Ahmed-Husseini/Automated-Robot-Arm/Media/1.jpg

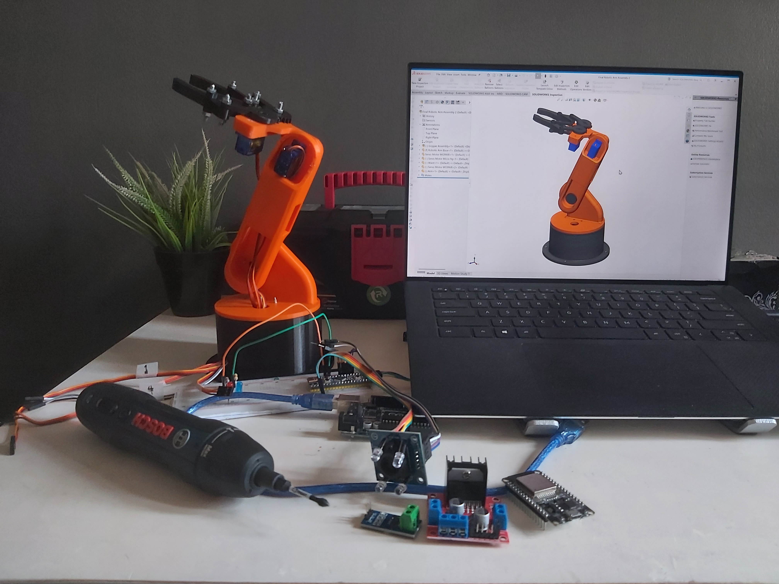
Media/1.jpg
