Ahmed-Husseini/Automated-Robot-Arm/Media/2.jpg

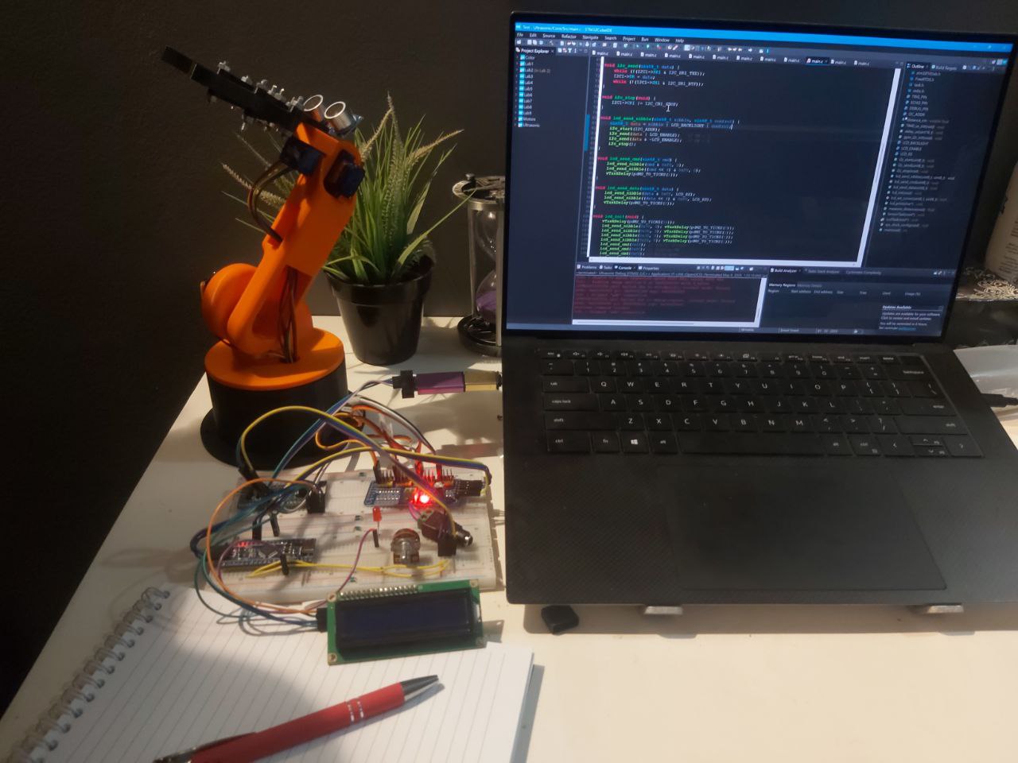
Media/2.jpg
