Ahmed-Husseini/Automated-Robot-Arm/Media/7.jpg

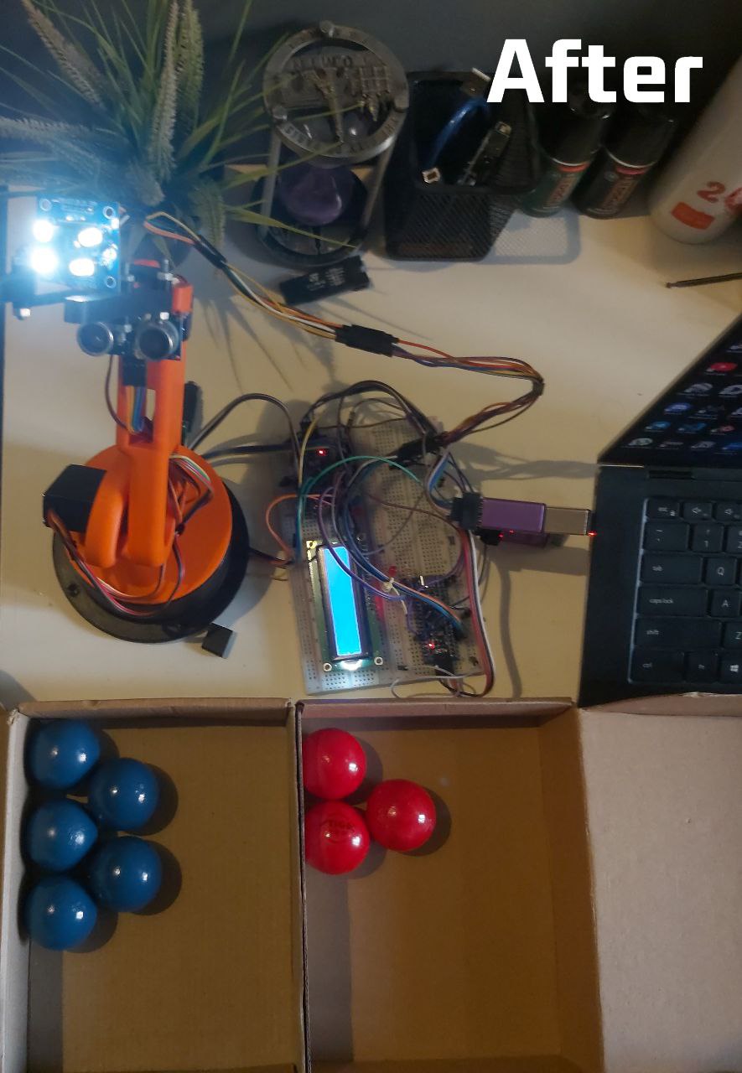
Media/7.jpg
