Ahmed-Husseini/Automated-Robot-Arm/Model/Images/Drawing.JPG

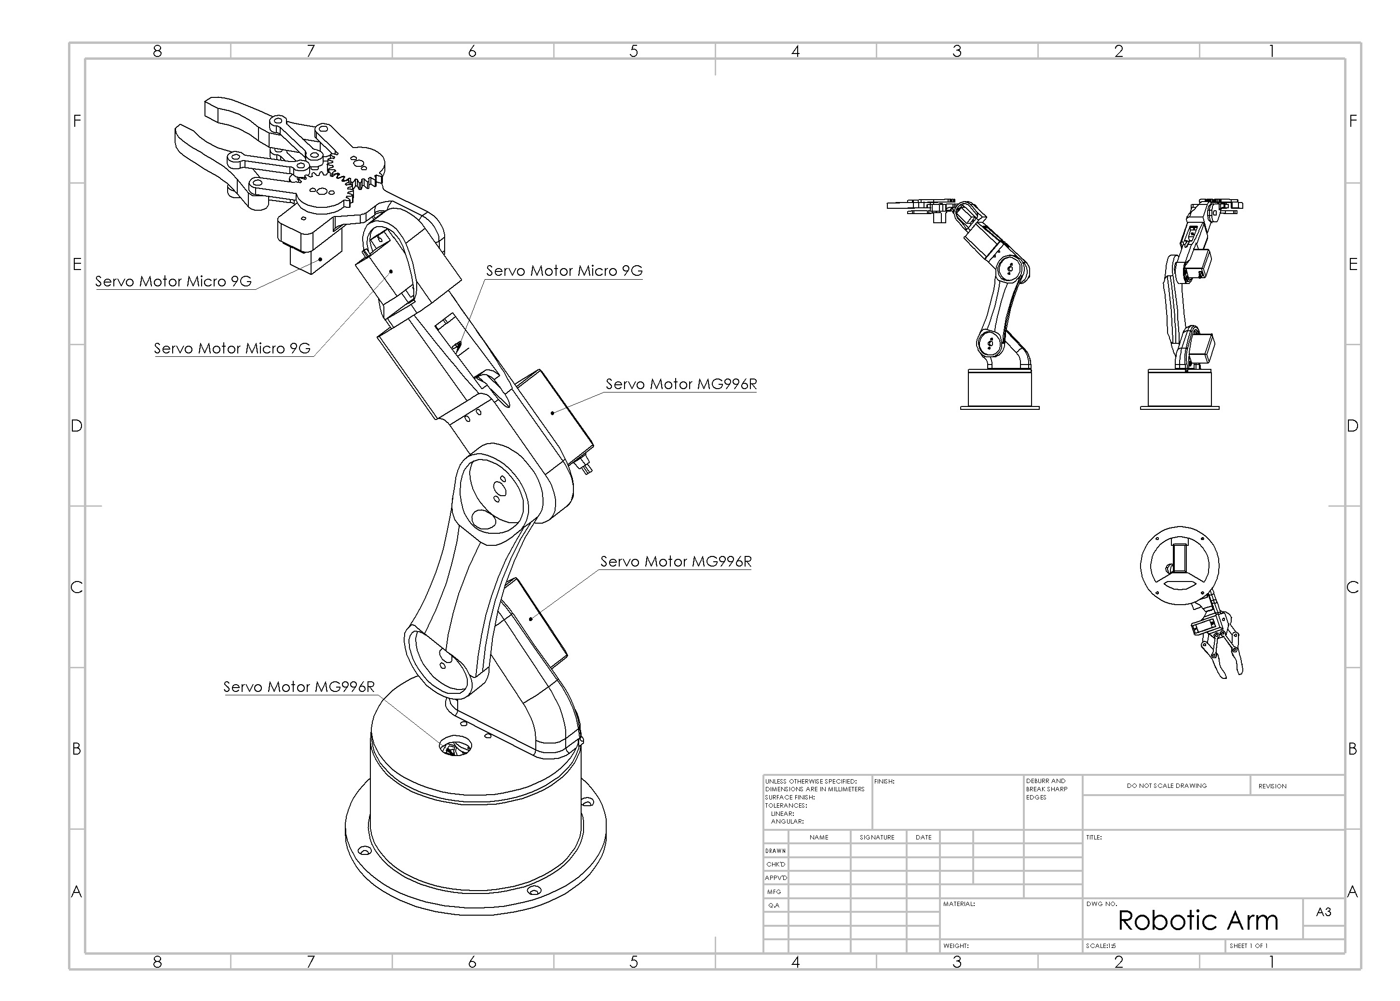
Model/Images/Drawing.JPG
