Ahmed-Husseini/Automated-Robot-Arm/Model/STL Files/Gripper 1.STL

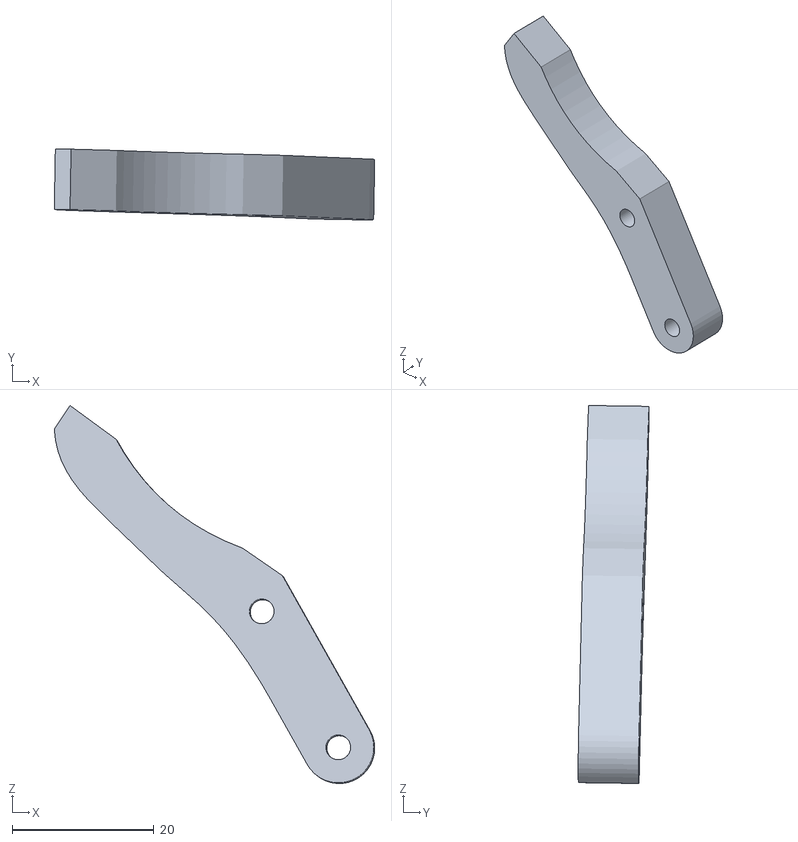
[picture p42: CAD file, 2025-07-17]
Model/STL Files/Gripper 1.STL
45.2 x 9.97 x 53.3
