Ahmed-Husseini/Automated-Robot-Arm/Model/Servo Motor Micro 9g.SLDPRT

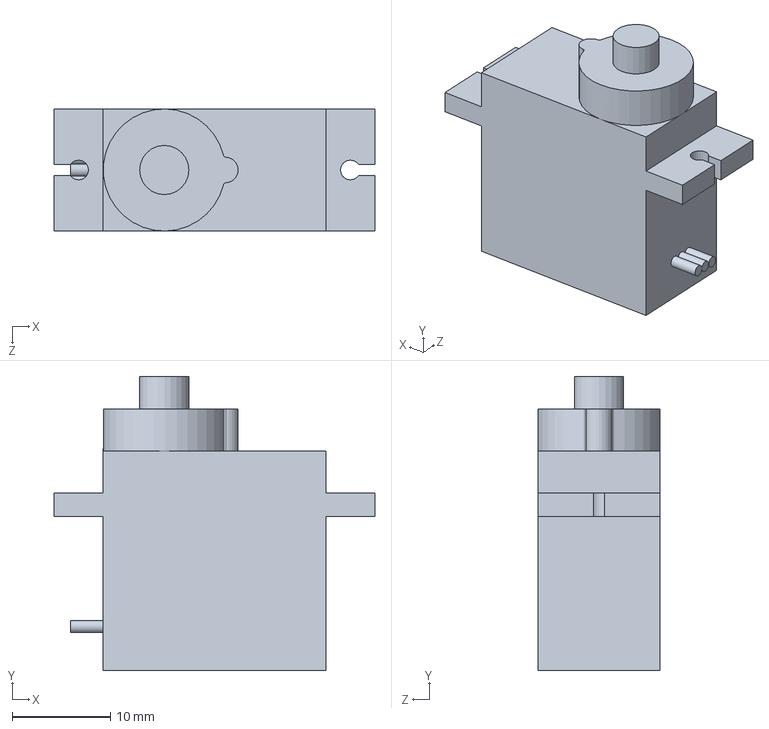
[picture p43: CAD file, 2025-07-17]
Model/Servo Motor Micro 9g.SLDPRT
32.6 x 29.9 x 12.4 mm
