Ahmed-Husseini/Automated-Robot-Arm/Model/Arm 3.SLDPRT

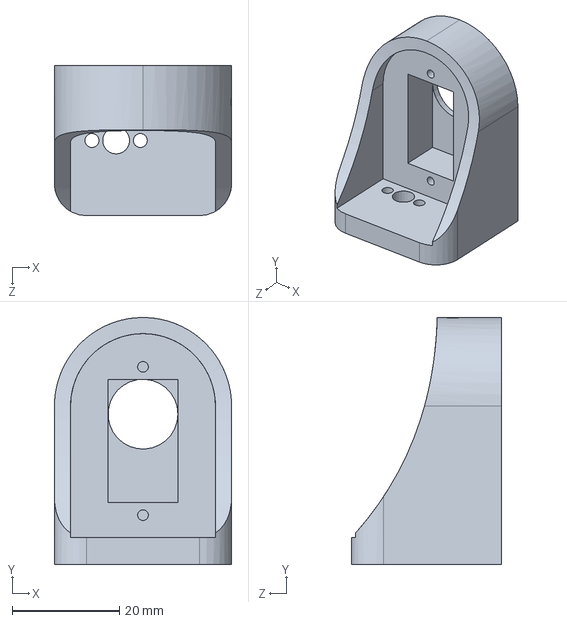
[picture p44: CAD file, 2025-07-17]
Model/Arm 3.SLDPRT
33.0 x 46.0 x 28.0 mm
