Ahmed-Husseini/Automated-Robot-Arm/Model/Arm 2.SLDPRT

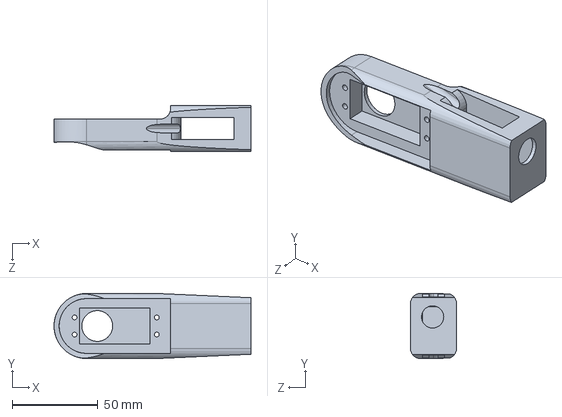
[picture p45: CAD file, 2025-07-17]
Model/Arm 2.SLDPRT
115.0 x 38.0 x 27.0 mm
