Ahmed-Husseini/Automated-Robot-Arm/Model/Waist.SLDPRT

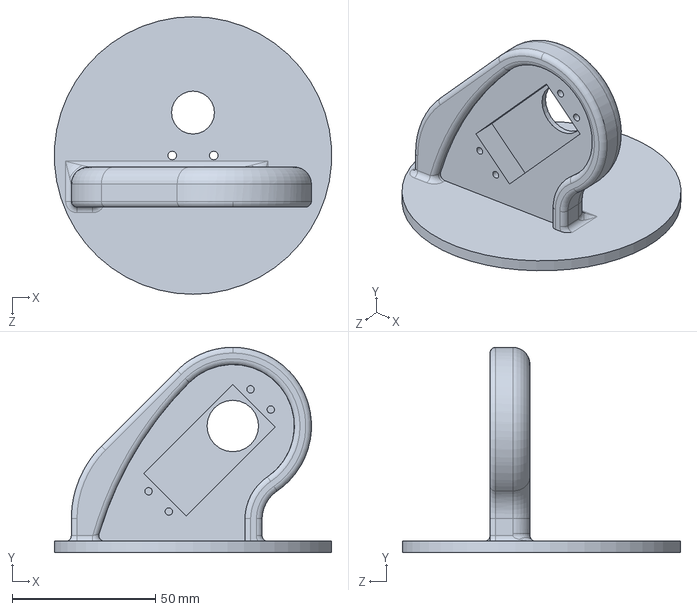
[picture p46: CAD file, 2025-07-17]
Model/Waist.SLDPRT
96.8 x 71.8 x 97.0 mm
