Ahmed-Husseini/Automated-Robot-Arm/Model/Arm 1.SLDPRT

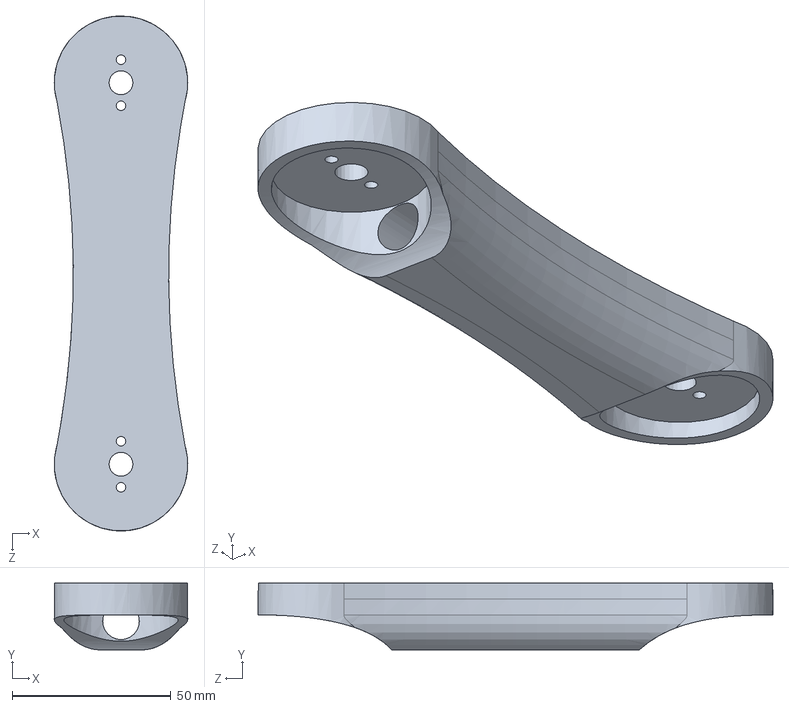
[picture p47: CAD file, 2025-07-17]
Model/Arm 1.SLDPRT
42.0 x 21.0 x 162.0 mm
