Ahmed-Husseini/Automated-Robot-Arm/Model/Gripper Base.SLDPRT

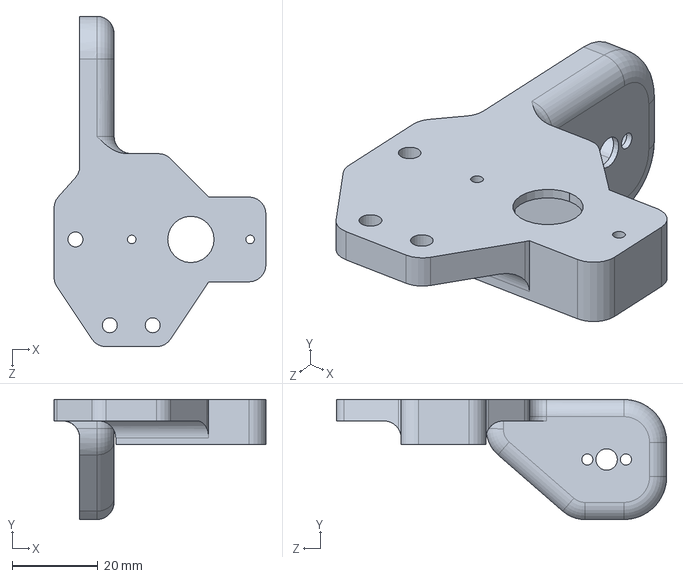
[picture p48: CAD file, 2025-07-17]
Model/Gripper Base.SLDPRT
49.4 x 28.0 x 77.0 mm
