Ahmed-Husseini/Automated-Robot-Arm/Model/Final Assembly 3D.JPG

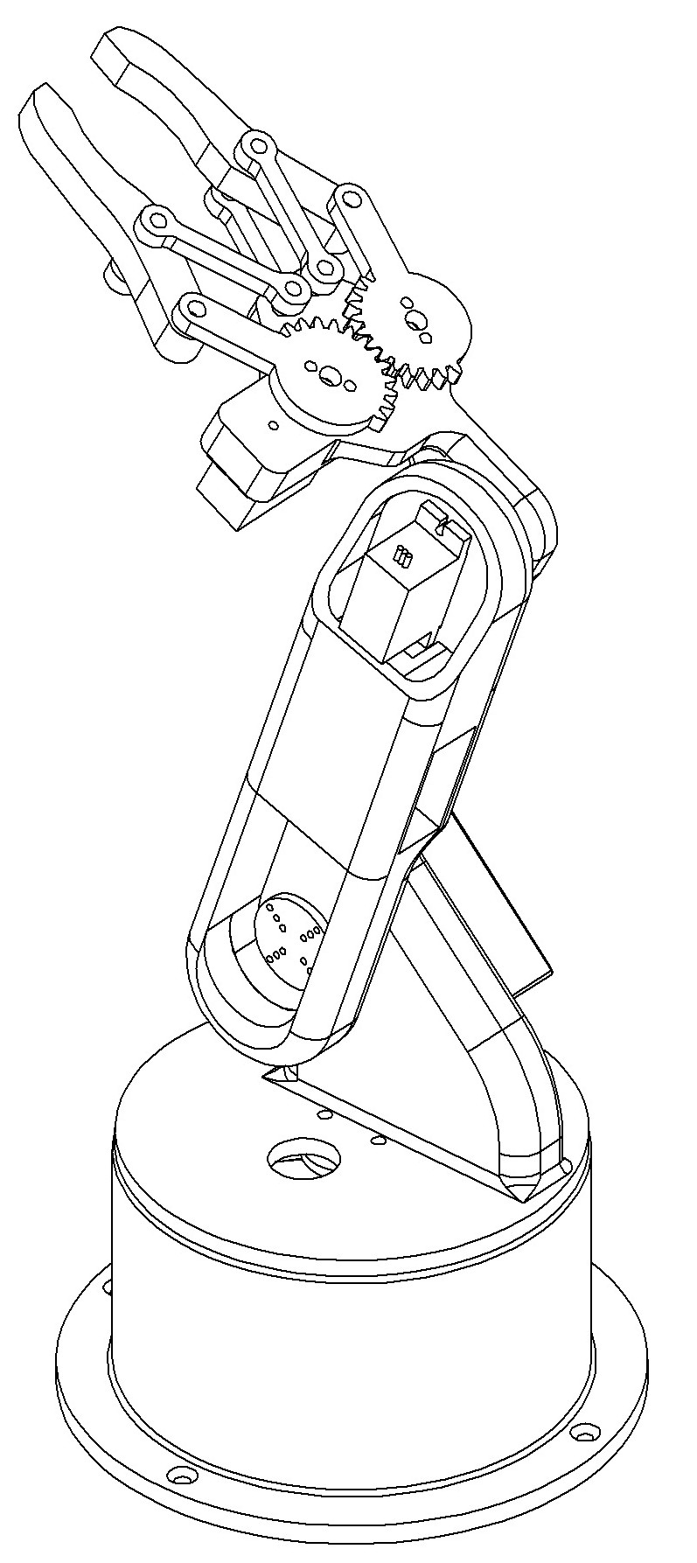
Model/Final Assembly 3D.JPG
