Ahmed-Husseini/Automated-Robot-Arm/Model/Final Assembly Bottom.JPG

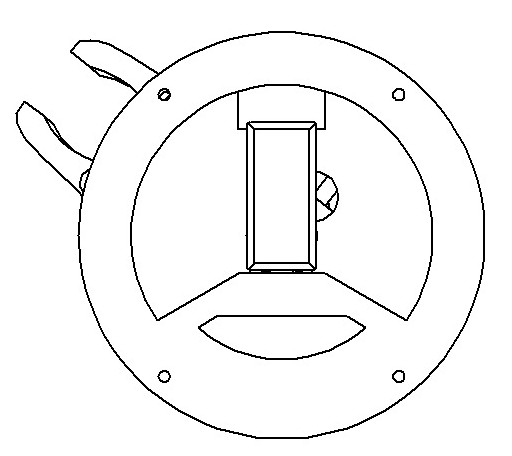
Model/Final Assembly Bottom.JPG
