Ahmed-Husseini/Automated-Robot-Arm/Model/Final Assembly Flip.JPG

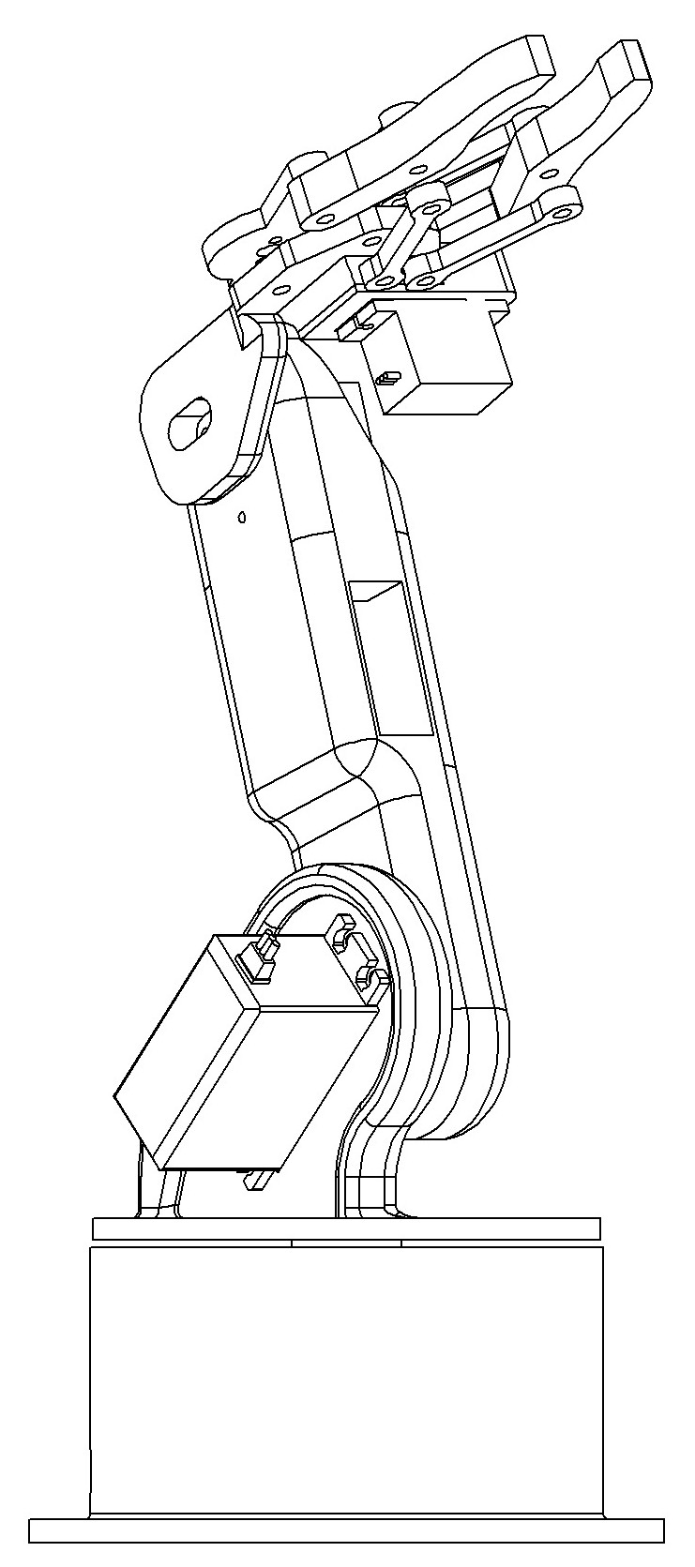
Model/Final Assembly Flip.JPG
