Ahmed-Husseini/Automated-Robot-Arm/Model/Final Assembly.JPG

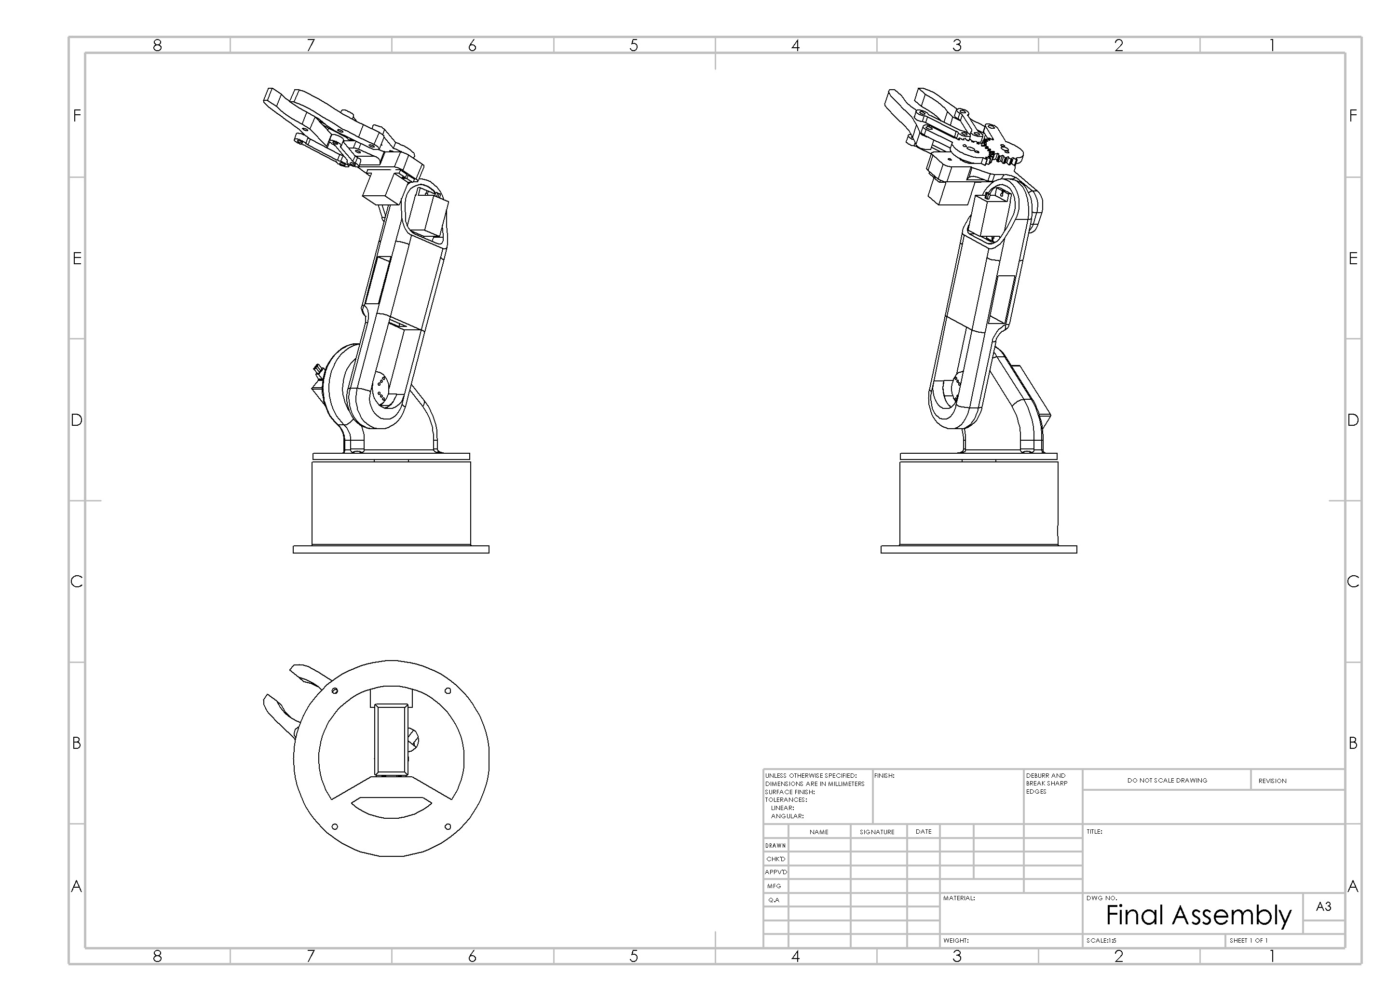
Model/Final Assembly.JPG
